cva68/Odometer-Amplifier/KiCad/Odometer-Amplifier.kicad_sch

## KiCad design KiCad/Odometer-Amplifier.kicad_sch (2025-06-08, an earlier design)

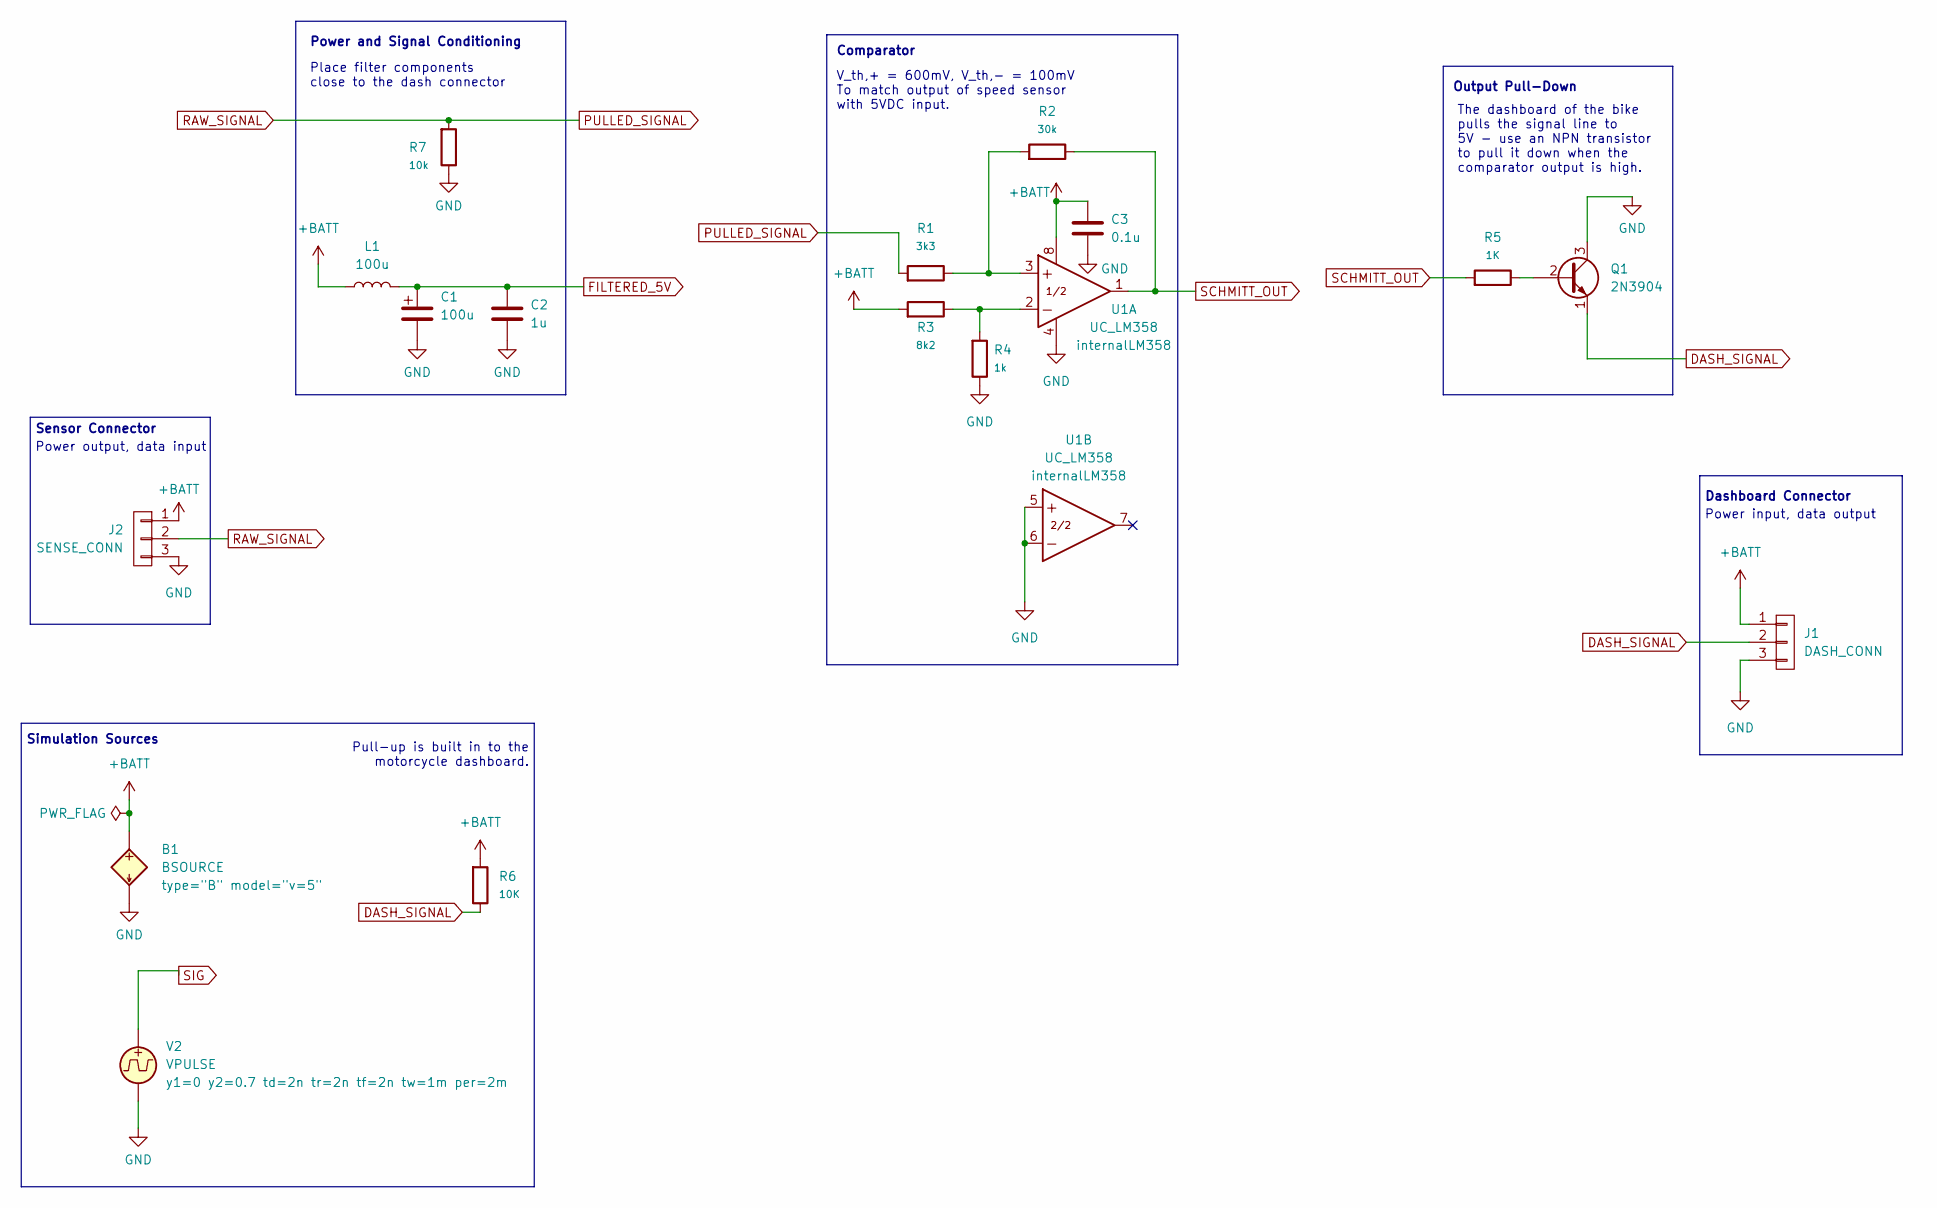
[picture p3: schematic Odometer-Amplifier.kicad_sch]

Parts:
B1: BSOURCE
C1: 100u; CP_Radial_D5.0mm_P2.00mm
C2: 1u; C_Rect_L7.0mm_W2.5mm_P5.00mm
C3: 0.1u; C_Rect_L7.0mm_W2.5mm_P5.00mm
J1: DASH_CONN; PinHeader_1x03_P2.54mm_Vertical
J2: SENSE_CONN; PinHeader_1x03_P2.54mm_Vertical
L1: 100u; L_Axial_L6.6mm_D2.7mm_P2.54mm_Vertical_Vishay_IM-2
Q1: 2N3904; TO-92_Inline
R1: 3k3; R_Axial_DIN0207_L6.3mm_D2.5mm_P7.62mm_Horizontal
R2: 30k; R_Axial_DIN0207_L6.3mm_D2.5mm_P7.62mm_Horizontal
R3: 8k2; R_Axial_DIN0207_L6.3mm_D2.5mm_P7.62mm_Horizontal
R4: 1k; R_Axial_DIN0207_L6.3mm_D2.5mm_P7.62mm_Horizontal
R5: 1K; R_Axial_DIN0207_L6.3mm_D2.5mm_P7.62mm_Horizontal
R6: 10K; R_Axial_DIN0207_L6.3mm_D2.5mm_P7.62mm_Horizontal
R7: 10k; R_Axial_DIN0207_L6.3mm_D2.5mm_P7.62mm_Horizontal
U1: UC_LM358; DIP-8_W7.62mm_LongPads
V2: VPULSE

Connections:
+BATT: B1.1 (N+), C3.1, J1.1, J2.1, L1.1, R3.1, R6.1, U1.8 (V+)
DASH_SIGNAL: J1.2, Q1.1 (E), R6.2
FILTERED_5V: C1.1, C2.1, L1.2
GND: B1.2 (N-), C1.2, C2.2, C3.2, J1.3, J2.3, Q1.3 (C), R4.2, R7.2, U1.4 (V-), U1.5 (+), U1.6 (-), V2.2
unnamed: Q1.2 (B), R5.2
unnamed: R1.2, R2.1, U1.3 (+)
unnamed: R3.2, R4.1, U1.2 (-)
PULLED_SIGNAL: J2.2, R1.1, R7.1
SCHMITT_OUT: R2.2, R5.1, U1.1
SIG: V2.1

Notes on the sheet:
Power and Signal Conditioning
Sensor Connector
Comparator
Dashboard Connector
The dashboard of the bike pulls the signal line to 5V - use an NPN transistor to pull it down when the comparator output is high.
Power input, data output
Power output, data input
Output Pull-Down
V_th,+ = 600mV, V_th,- = 100mV To match output of speed sensor with 5VDC input.
Place filter components close to the dash connector
Simulation Sources
Pull-up is built in to the motorcycle dashboard.
